durki007/smart-compass/hardware/compass-final/compass-final.kicad_sch

## KiCad design hardware/compass-final/compass-final.kicad_sch (2024-05-26, an earlier design)

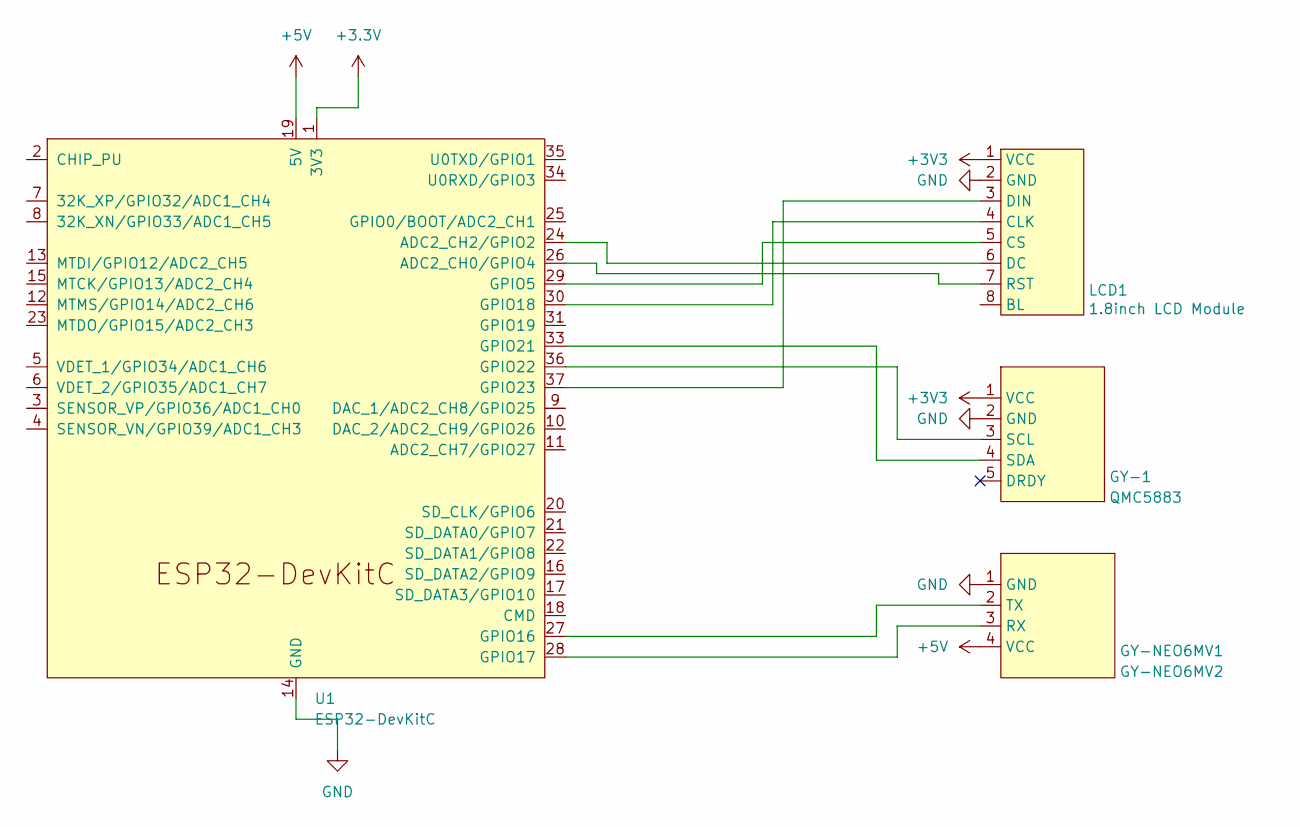
[picture p24: schematic compass-final.kicad_sch]

Parts:
GY-1: QMC5883
GY-NEO6MV1: GY-NEO6MV2
LCD1: 1.8inch LCD Module
U1: ESP32-DevKitC

Connections:
+3.3V: U1.1 (3V3)
+3V3: GY-1.1 (VCC), LCD1.1 (VCC)
+5V: GY-NEO6MV1.4 (VCC), U1.19 (5V)
GND: GY-1.2 (GND), GY-NEO6MV1.1 (GND), LCD1.2 (GND), U1.14 (GND), U1.32 (GND), U1.38 (GND)
unnamed: GY-1.3 (SCL), U1.36 (GPIO22)
unnamed: GY-1.4 (SDA), U1.33 (GPIO21)
unnamed: GY-NEO6MV1.2 (TX), U1.27 (GPIO16)
unnamed: GY-NEO6MV1.3 (RX), U1.28 (GPIO17)
unnamed: LCD1.3 (DIN), U1.37 (GPIO23)
unnamed: LCD1.4 (CLK), U1.30 (GPIO18)
unnamed: LCD1.5 (CS), U1.29 (GPIO5)
unnamed: LCD1.6 (DC), U1.24 (ADC2_CH2/GPIO2)
unnamed: LCD1.7 (RST), U1.26 (ADC2_CH0/GPIO4)
