durki007/smart-compass/hardware/ki-cad/compass-schematics.kicad_sch

## KiCad design hardware/ki-cad/compass-schematics.kicad_sch (2024-04-07)

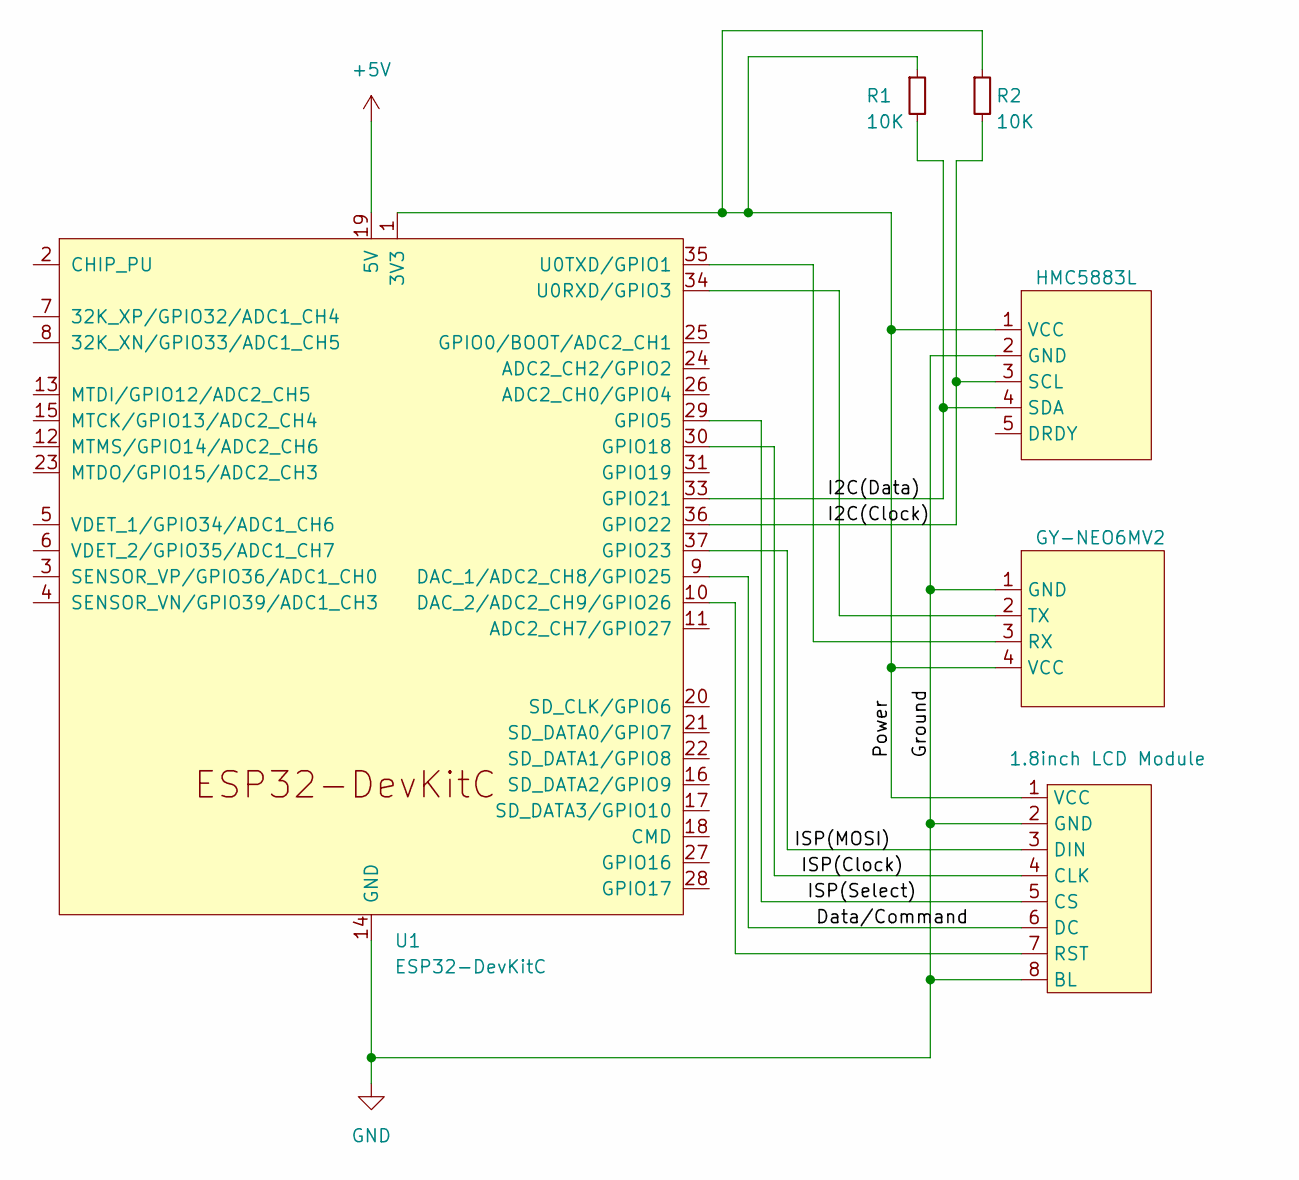
[picture p25: schematic compass-schematics.kicad_sch]

Parts:
GY-1: HMC5883L
GY-NEO6MV1: GY-NEO6MV2
LCD1: 1.8inch LCD Module
R1, R2: 10K
U1: ESP32-DevKitC

Connections:
+5V: U1.19 (5V)
Data/Command: LCD1.6 (DC), U1.9 (DAC_1/ADC2_CH8/GPIO25)
GND: GY-1.2 (GND), GY-NEO6MV1.1 (GND), LCD1.2 (GND), LCD1.8 (BL), U1.14 (GND), U1.32 (GND), U1.38 (GND)
I2C(Clock): GY-1.3 (SCL), R2.2, U1.36 (GPIO22)
I2C(Data): GY-1.4 (SDA), R1.2, U1.33 (GPIO21)
ISP(Clock): LCD1.4 (CLK), U1.30 (GPIO18)
ISP(MOSI): LCD1.3 (DIN), U1.37 (GPIO23)
ISP(Select): LCD1.5 (CS), U1.29 (GPIO5)
unnamed: GY-NEO6MV1.2 (TX), U1.34 (U0RXD/GPIO3)
unnamed: GY-NEO6MV1.3 (RX), U1.35 (U0TXD/GPIO1)
unnamed: LCD1.7 (RST), U1.10 (DAC_2/ADC2_CH9/GPIO26)
Power: GY-1.1 (VCC), GY-NEO6MV1.4 (VCC), LCD1.1 (VCC), R1.1, R2.1, U1.1 (3V3)
